puttersp/robknob/cad/nutm5.SLDPRT

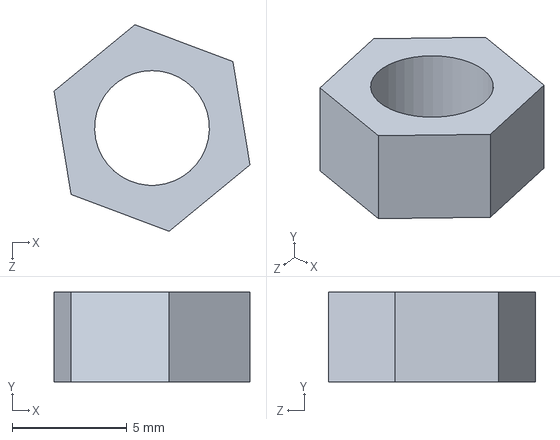
[picture p17: CAD file, 2024-01-09]
cad/nutm5.SLDPRT
8.54 x 3.90 x 9.00 mm
