puttersp/robknob/cad/slipring_src022a12.SLDPRT

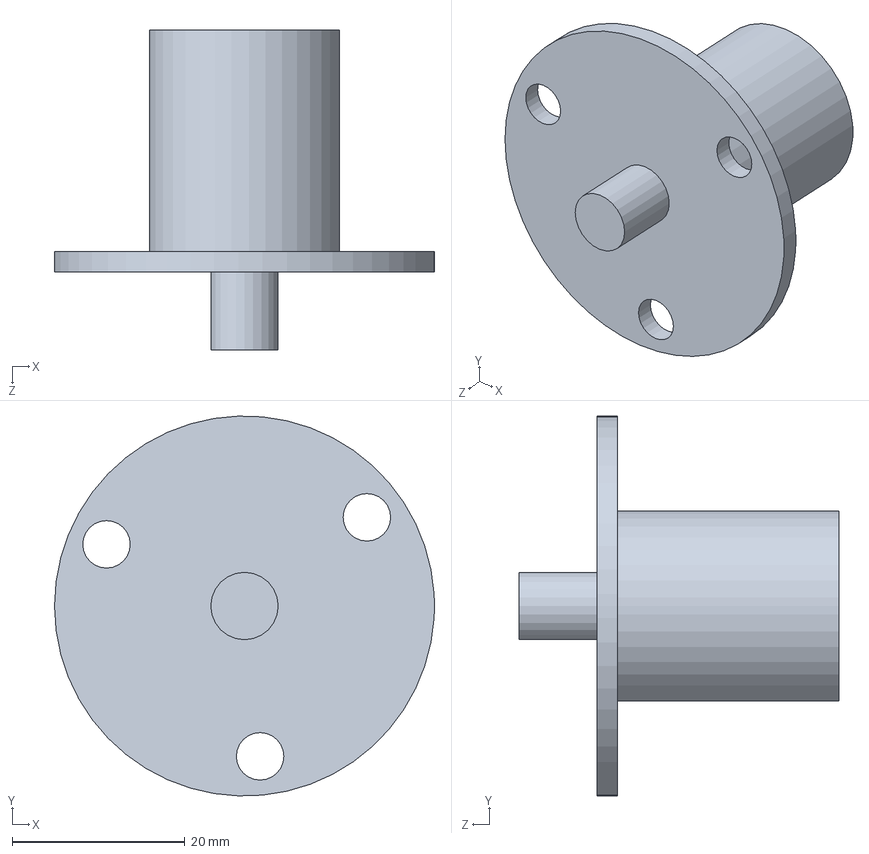
[picture p18: CAD file, 2024-01-09]
cad/slipring_src022a12.SLDPRT
44.0 x 44.0 x 37.0 mm
