puttersp/robknob/cad/knob.SLDPRT

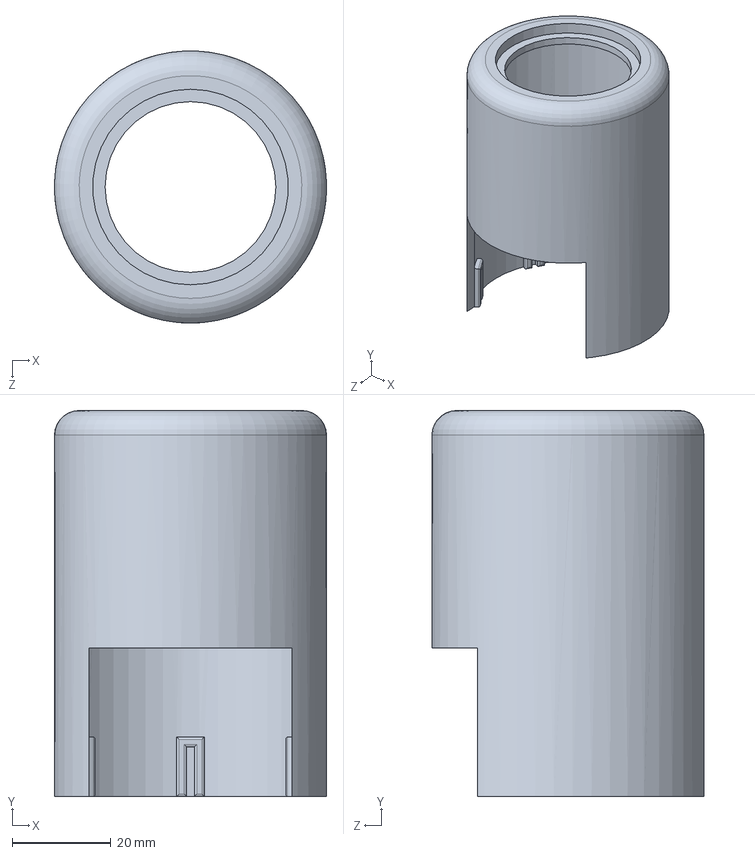
[picture p19: CAD file, 2024-01-09]
cad/knob.SLDPRT
55.0 x 78.0 x 55.0 mm
