puttersp/robknob/cad/m5.SLDPRT

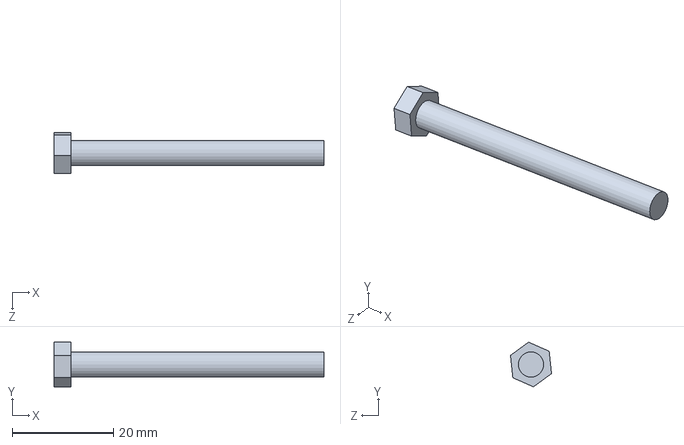
[picture p20: CAD file, 2024-01-09]
cad/m5.SLDPRT
53.4 x 8.84 x 8.13 mm
