puttersp/robknob/cad/RotorSpacer.step

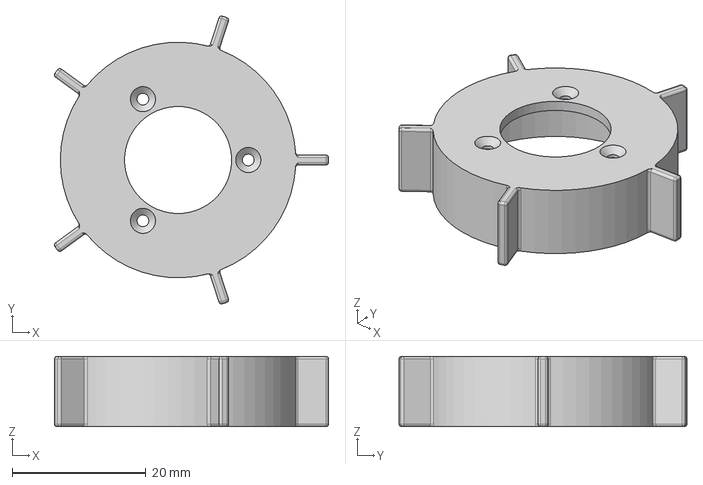
[picture p21: CAD file, 2024-01-09]
cad/RotorSpacer.step
41.0 x 43.0 x 10.5 mm
