puttersp/robknob/cad/ScreenPlatform.step

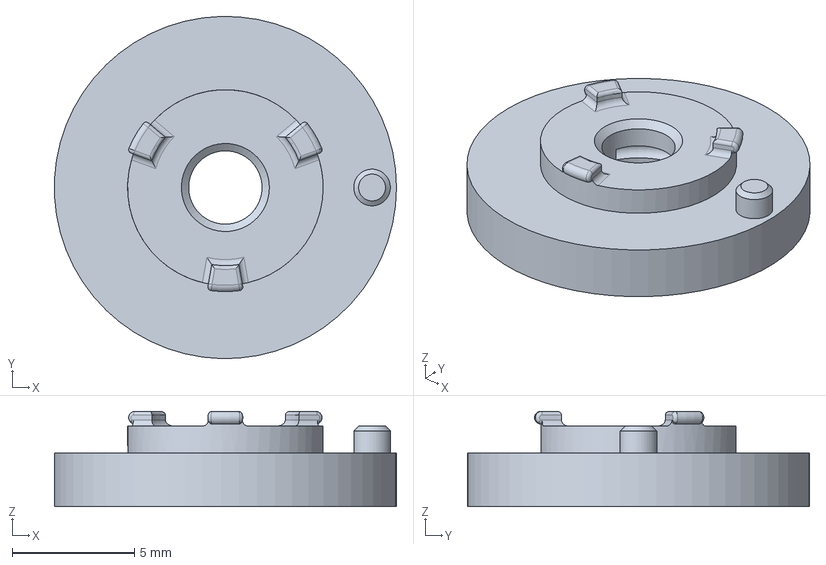
[picture p22: CAD file, 2024-01-09]
cad/ScreenPlatform.step
14.0 x 14.0 x 3.90 mm
