puttersp/robknob/cad/Glass.step

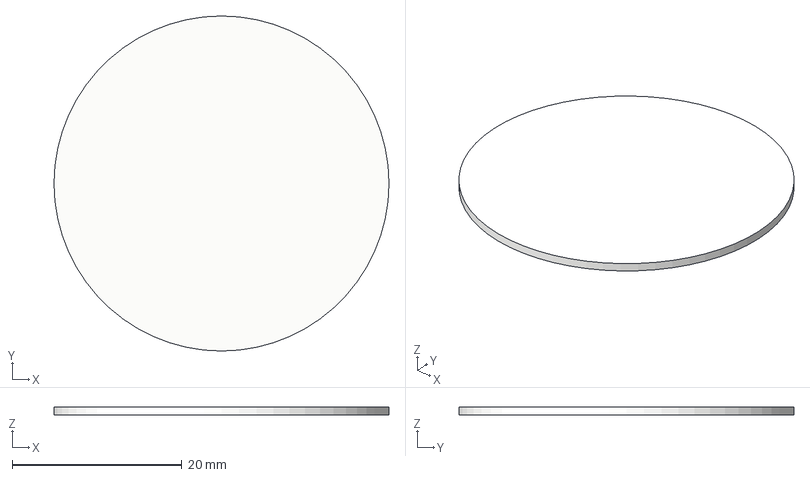
[picture p23: CAD file, 2024-01-09]
cad/Glass.step
39.5 x 39.5 x 1.00 mm
