puttersp/robknob/cad/LidarMount.SLDPRT

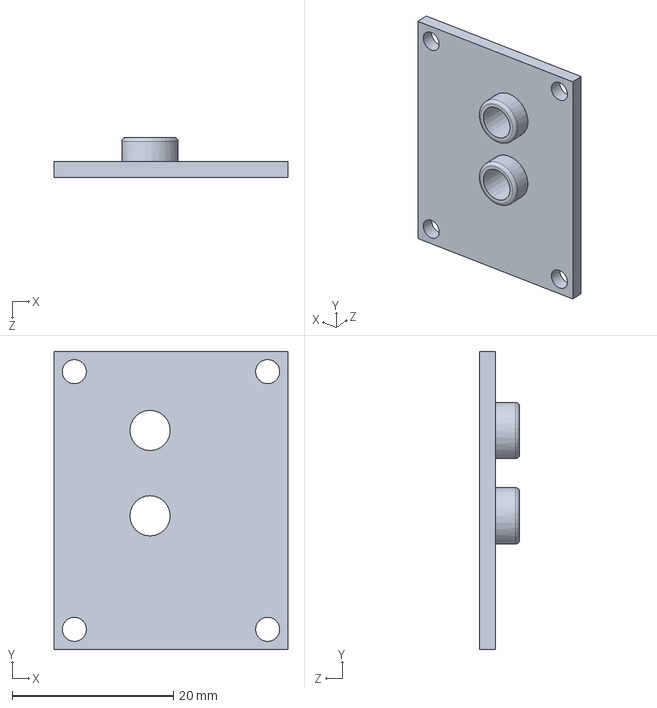
[picture p24: CAD file, 2024-01-09]
cad/LidarMount.SLDPRT
29.0 x 37.0 x 5.00 mm
