puttersp/robknob/cad/MountBaseLongPart.SLDPRT

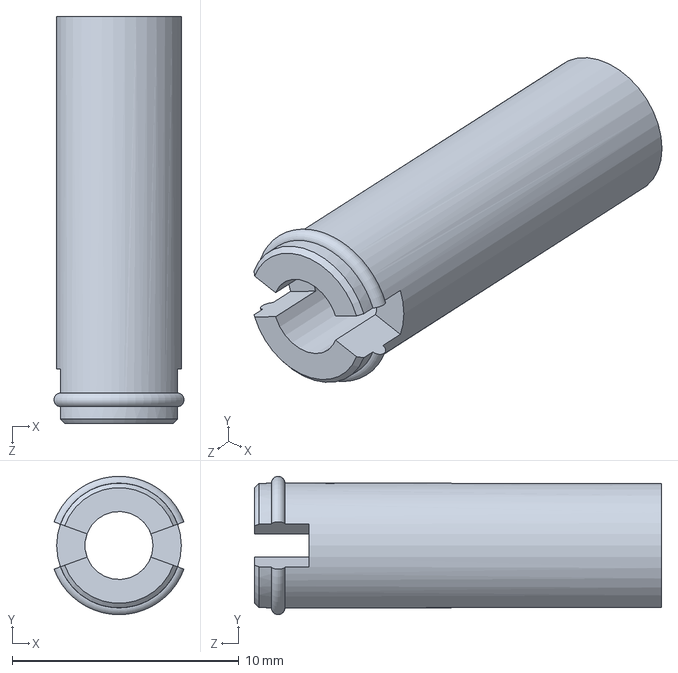
[picture p25: CAD file, 2024-01-09]
cad/MountBaseLongPart.SLDPRT
5.73 x 6.10 x 18.0 mm
