puttersp/robknob/cad/RotorSpacerNew.SLDPRT

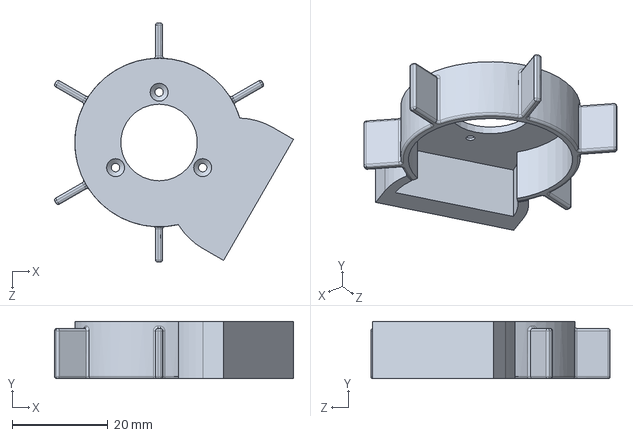
[picture p26: CAD file, 2024-01-09]
cad/RotorSpacerNew.SLDPRT
49.9 x 12.0 x 50.0 mm
