puttersp/robknob/cad/SlipRingPlatform.SLDPRT

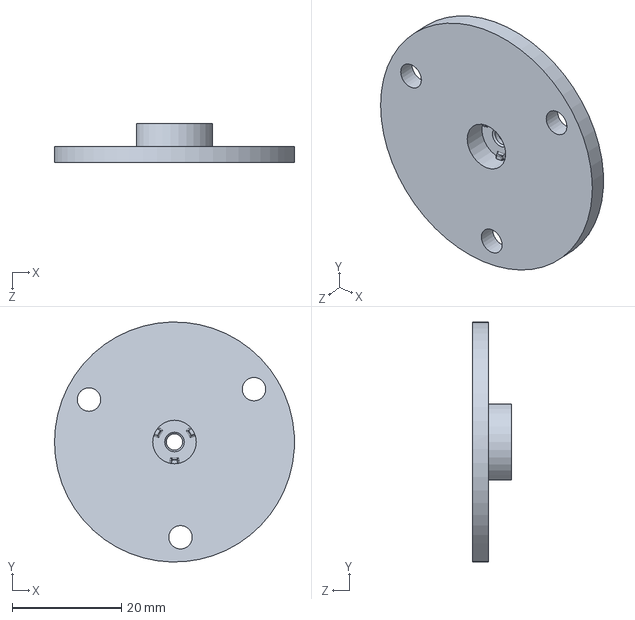
[picture p27: CAD file, 2024-01-09]
cad/SlipRingPlatform.SLDPRT
44.0 x 44.0 x 7.20 mm
