puttersp/robknob/cad/ScreenPCB.step

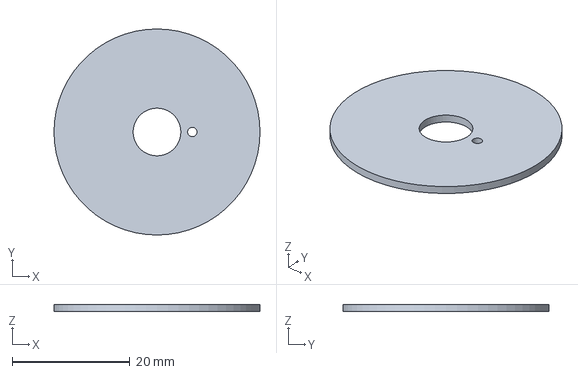
[picture p28: CAD file, 2024-01-09]
cad/ScreenPCB.step
35.0 x 35.0 x 1.20 mm
