puttersp/robknob/cad/conn_stat2.SLDPRT

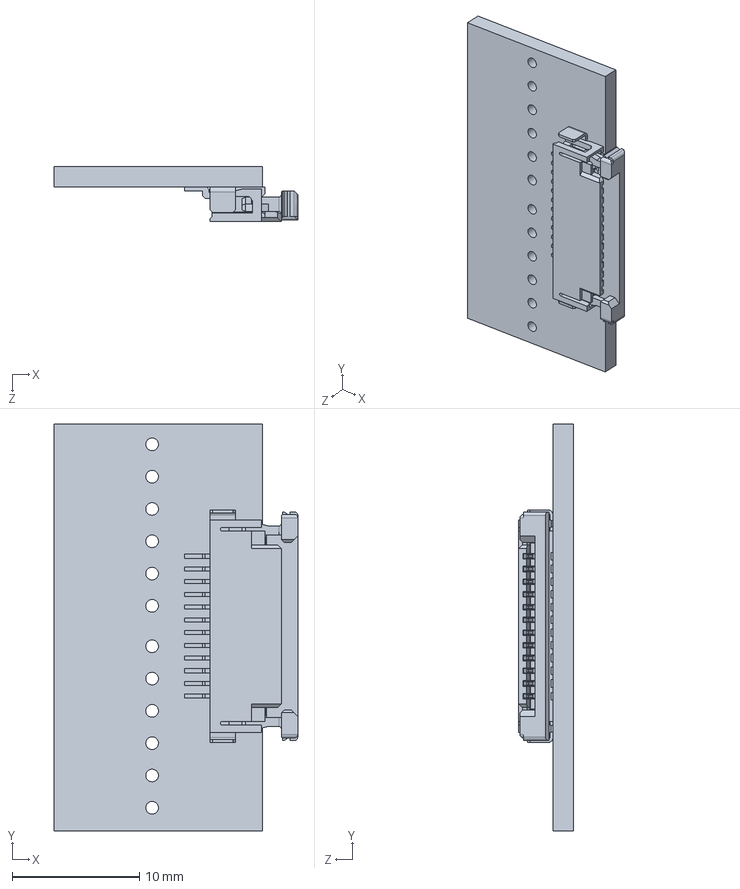
[picture p29: CAD file, 2024-01-09]
cad/conn_stat2.SLDPRT
19.2 x 32.0 x 4.30 mm
