puttersp/robknob/cad/MountBaseBasePart.SLDPRT

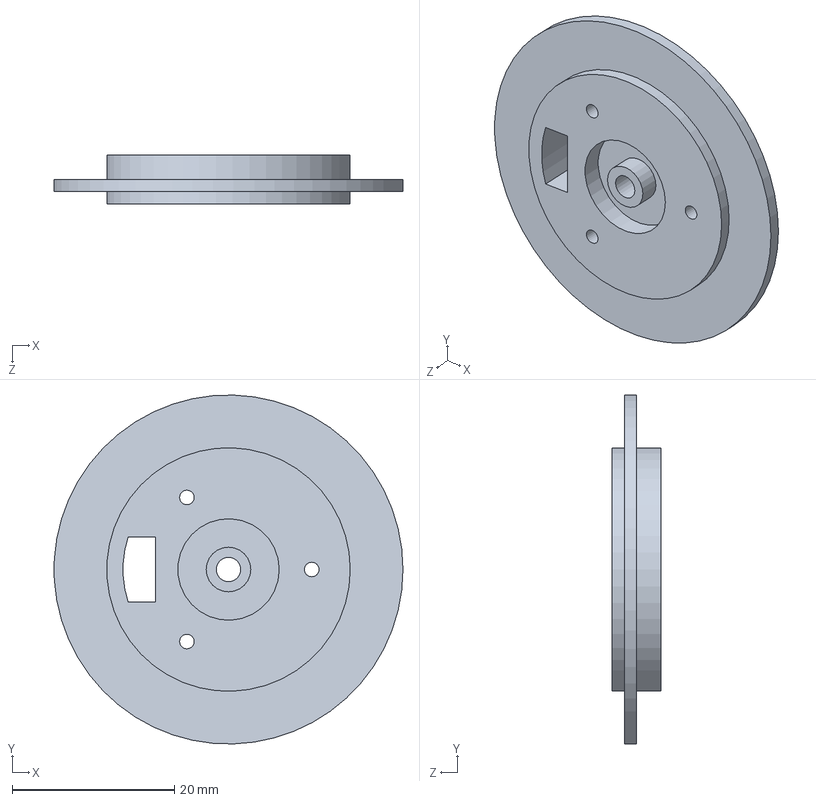
[picture p30: CAD file, 2024-01-09]
cad/MountBaseBasePart.SLDPRT
43.0 x 43.0 x 6.00 mm
