puttersp/robknob/cad/BLDCMotor.step

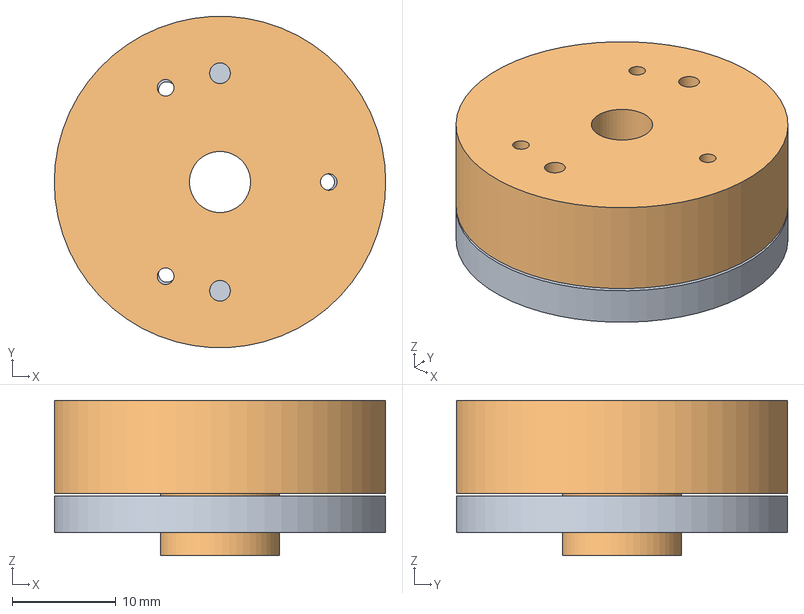
[picture p31: CAD file, 2023-11-23]
cad/BLDCMotor.step
32.0 x 32.0 x 15.0 mm
Stator
Rotor
