puttersp/robknob/cad/slip ring.SLDPRT

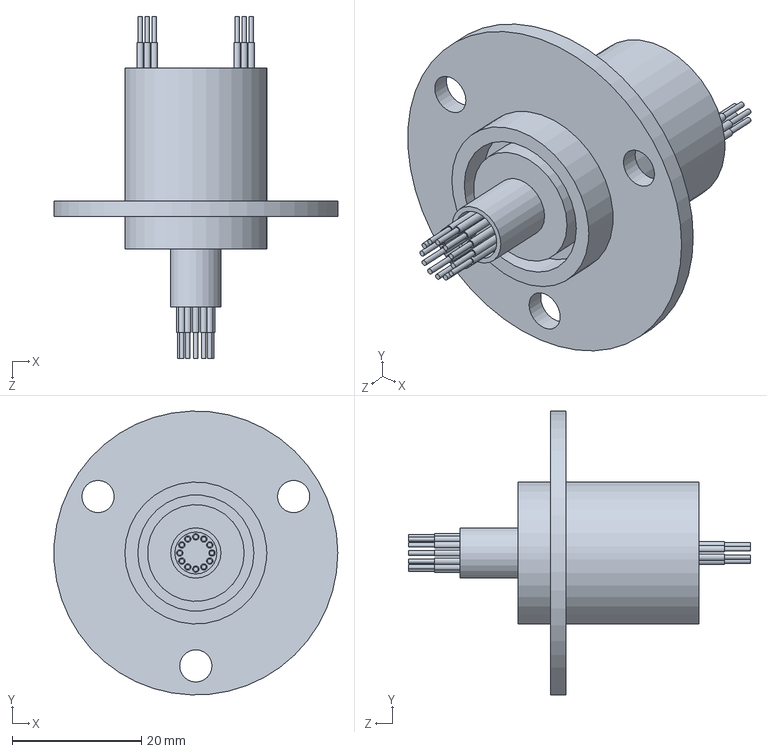
[picture p32: CAD file, 2023-11-23]
cad/slip ring.SLDPRT
44.0 x 44.0 x 53.0 mm
