puttersp/robknob/cad/Enclosure.step

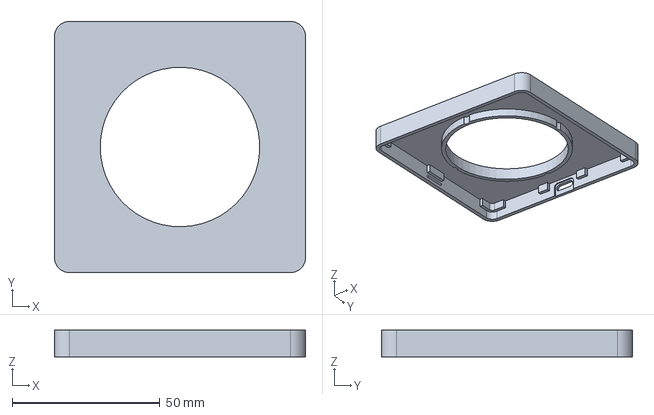
[picture p33: CAD file, 2023-11-23]
cad/Enclosure.step
85.0 x 85.0 x 9.00 mm
