puttersp/robknob/cad/BackPlate.step

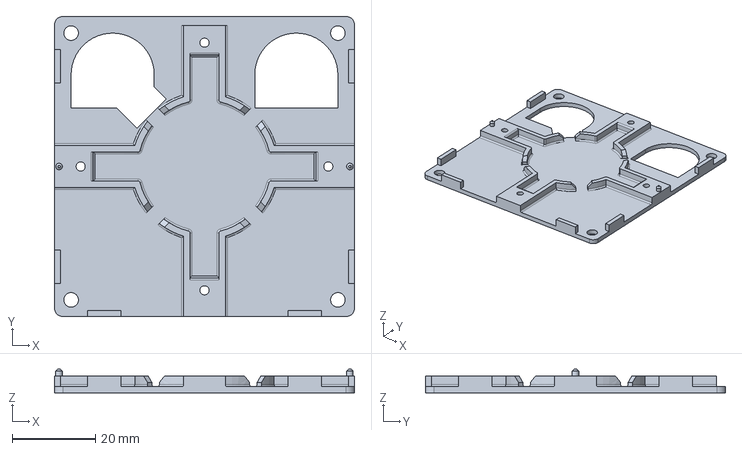
[picture p34: CAD file, 2023-11-23]
cad/BackPlate.step
72.2 x 72.2 x 5.70 mm
