puttersp/robknob/cad/MountBase.step

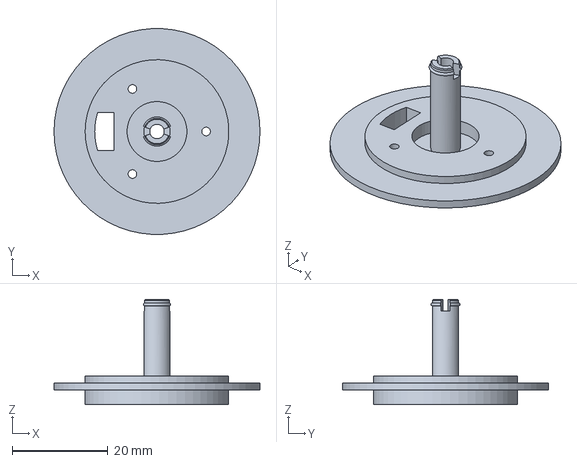
[picture p35: CAD file, 2023-11-23]
cad/MountBase.step
43.0 x 42.9 x 21.9 mm
