puttersp/robknob/firmware/robknob_stm32/Core/Inc/hardware_api.h

/*
 * hardware_api.h
 *
 *  Created on: Jan 10, 2024
 *      Author: putte
 */

#ifndef INC_HARDWARE_API_H_
#define INC_HARDWARE_API_H_

 #include "foc_utils.h"
 #include "time_utils.h"

 extern TIM_HandleTypeDef htim1;
 extern TIM_HandleTypeDef htim3;

 int _configure6PWM(long pwm_frequency, float dead_zone, const int pinA_h, const int pinA_l,  const int pinB_h, const int pinB_l, const int pinC_h, const int pinC_l);

 void _writeDutyCycle6PWM(float dc_a,  float dc_b, float dc_c, float dead_zone, int pinA_h, int pinA_l, int pinB_h, int pinB_l, int pinC_h, int pinC_l);



#endif /* INC_HARDWARE_API_H_ */
