puttersp/robknob/firmware/robknob_stm32_cpp/Core/Inc/SimpleFOC_stm32.h

/*
 * SimpleFOC_stm32.h
 *
 *  Created on: Jan 10, 2024
 *      Author: putte
 */

#ifndef INC_SIMPLEFOC_STM32_H_
#define INC_SIMPLEFOC_STM32_H_

#include "BLDCMotor.h"
#include "MT6701SSI.h"
#include "BLDCDriver6PWM.h"

#endif /* INC_SIMPLEFOC_STM32_H_ */
